IronMan1405/MonoDeck/platform/platform_init.c

#include "platform_init.h"
#include "platform_config.h"

#include "pico/stdlib.h"
#include "hardware/i2c.h"
#include "hardware/gpio.h"
#include "hardware/adc.h"

void platform_init(void) {
    stdio_init_all();
    i2c_init(I2C_PORT, I2C_BAUDRATE);

    gpio_set_function(I2C_SDA_PIN, GPIO_FUNC_I2C);
    gpio_set_function(I2C_SCL_PIN, GPIO_FUNC_I2C);

    gpio_pull_up(I2C_SDA_PIN);
    gpio_pull_up(I2C_SCL_PIN);

    adc_init();
    adc_gpio_init(26);
    adc_select_input(0);

    const uint8_t buttons[] = {
        BTN_UP_PIN,
        BTN_DOWN_PIN,
        BTN_LEFT_PIN,
        BTN_RIGHT_PIN,
        BTN_A_PIN,
        BTN_B_PIN,
        BTN_SEL_PIN,
        BTN_START_PIN
    };

    const size_t button_count = sizeof(buttons) / sizeof(buttons[0]);

    for (int i = 0; i < button_count; i++) {
        gpio_init(buttons[i]);
        gpio_set_dir(buttons[i], GPIO_IN);
        gpio_pull_up(buttons[i]);
    }
}
